s-light/magic_crystal/export/magic_crystal_3d_batteries_horizontal.png

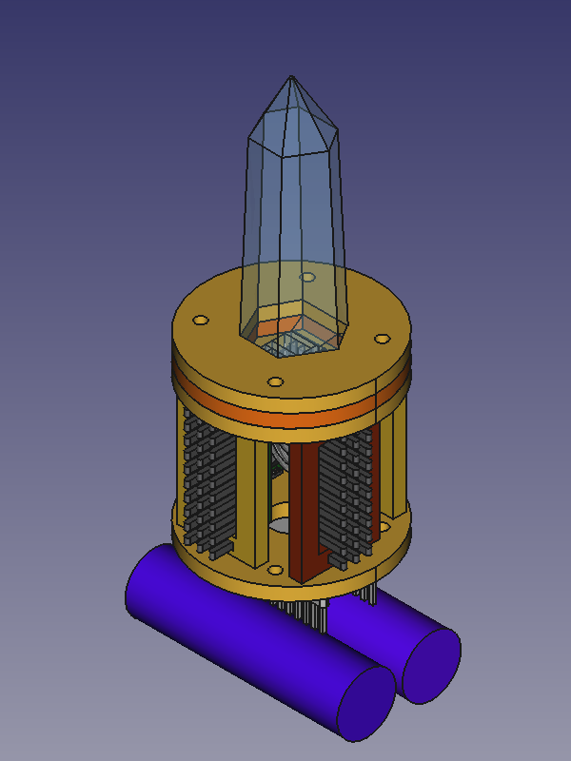
export/magic_crystal_3d_batteries_horizontal.png
