s-light/magic_crystal/export/magic_crystal_3d_batteries_vertical.png

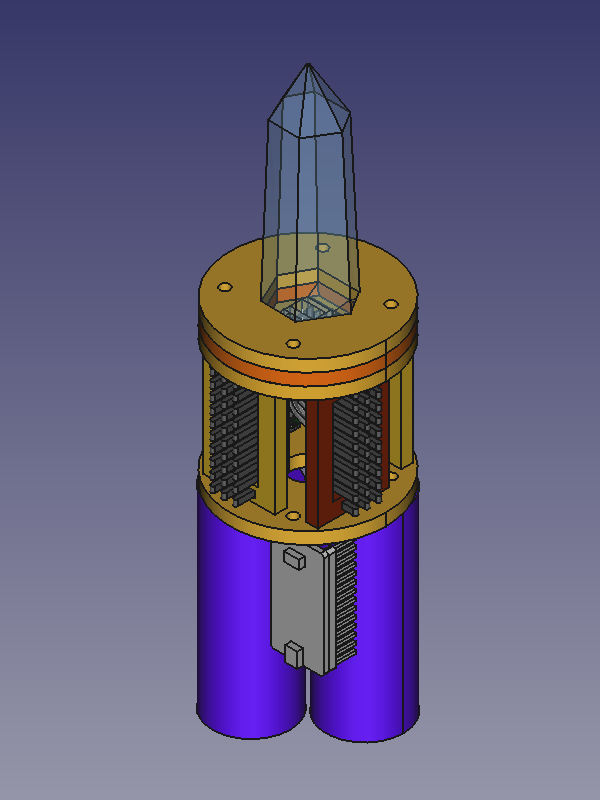
export/magic_crystal_3d_batteries_vertical.png
