s-light/magic_crystal/export/magic_crystal_3d_inside.png

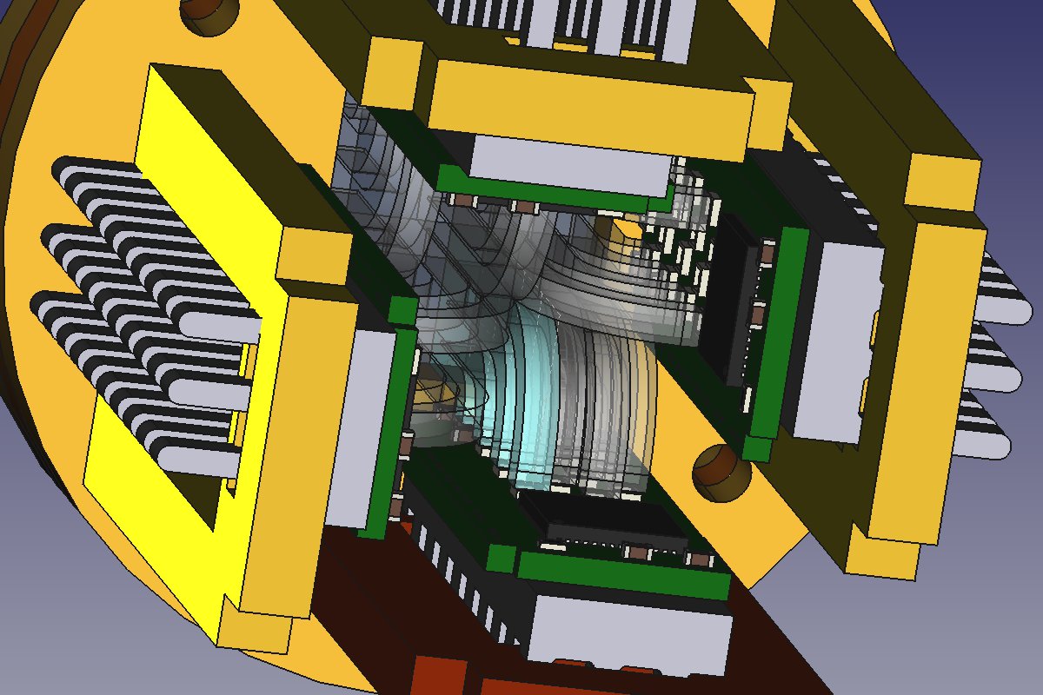
export/magic_crystal_3d_inside.png
